Shanker511/GateWatch/assets/concepts/09-demo-sequence-concept.png

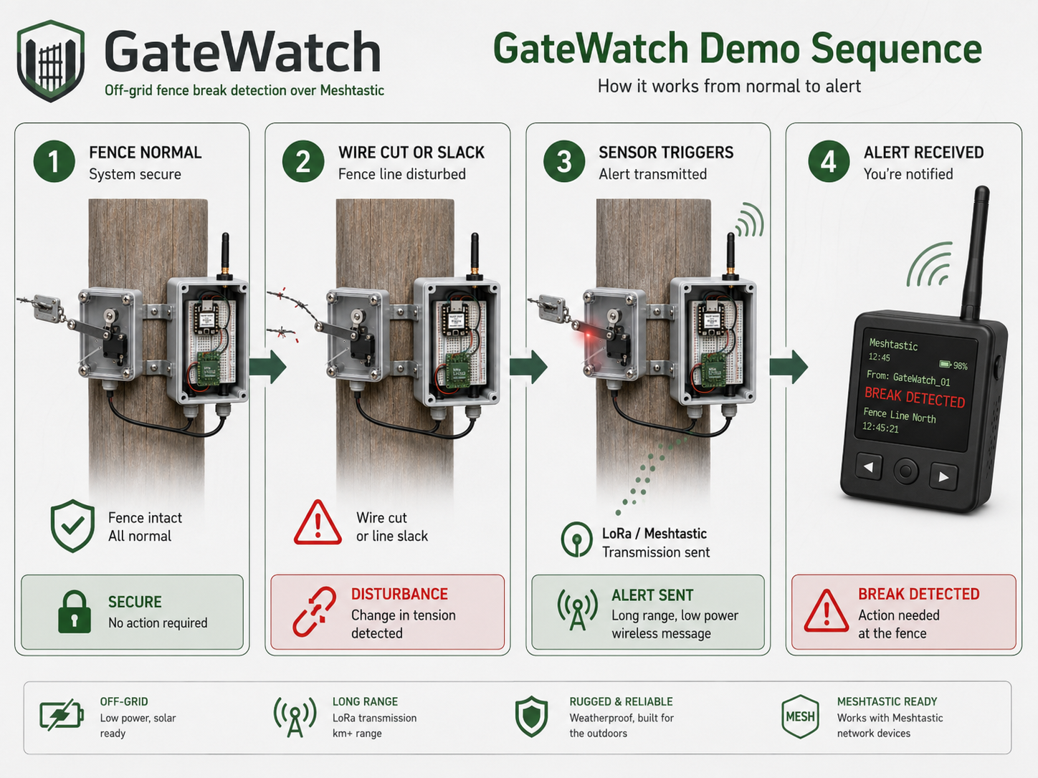
assets/concepts/09-demo-sequence-concept.png
