Shanker511/GateWatch/assets/concepts/10-farmer-use-concept.png

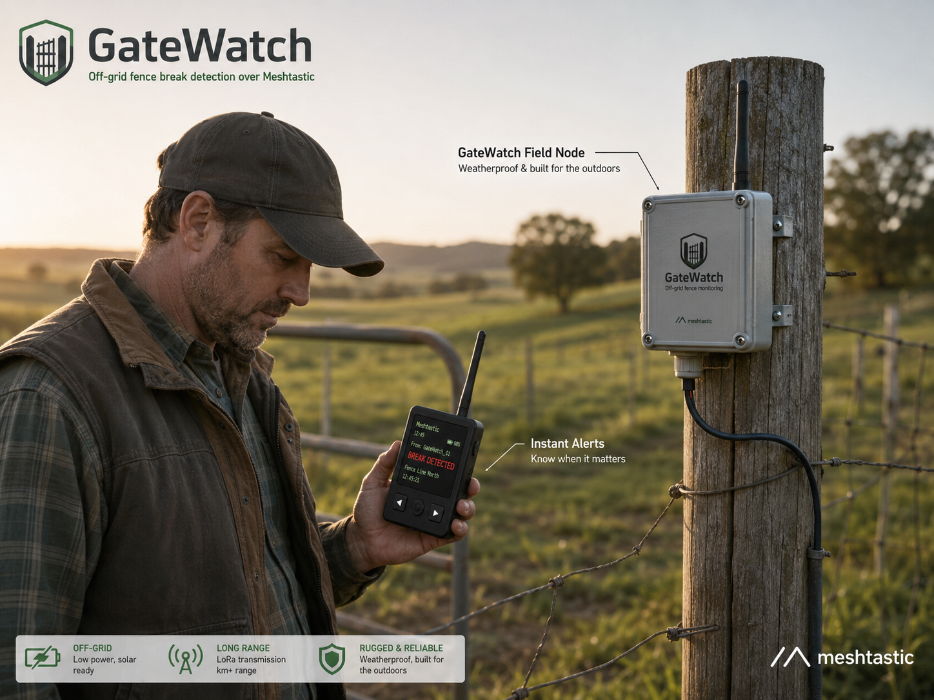
assets/concepts/10-farmer-use-concept.png
