Shanker511/GateWatch/assets/concepts/04-prototype-wiring-concept.png

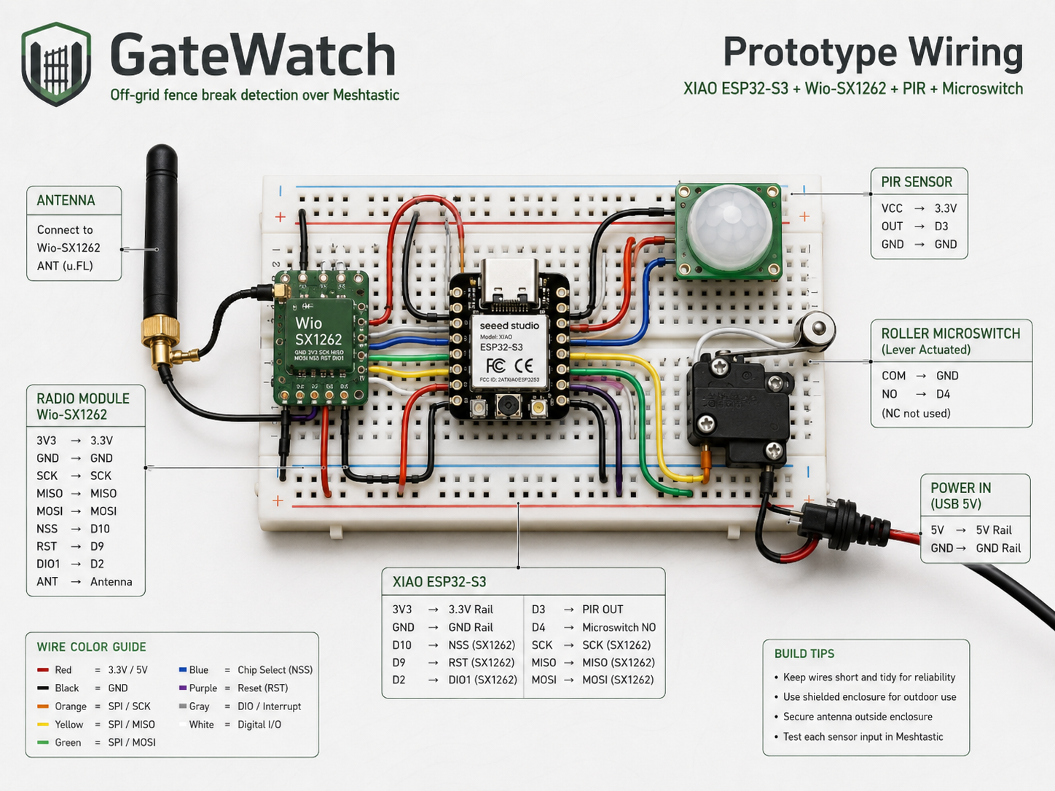
assets/concepts/04-prototype-wiring-concept.png
