Shanker511/GateWatch/hardware/gatewatch.kicad_sch

## KiCad design hardware/gatewatch.kicad_sch (2026-08-13)

Schematic: gatewatch.kicad_sch

Parts:
C1, C3, C4, C5, C6, C10: 100nF; C0805
C2, C7, C8, C9: 10uF; C0805
CN1: XT30UPB-M; CONN-TH_XT30UPB-M; MPN XT30UPB-M; LCSC C428721
CN2: B2B-PH-K-S; CONN-TH_B2B-PH-K-S; MPN B2B-PH-K-S(LF)(SN); LCSC C131337
D1: SS34_C8678; SMA_L4.3-W2.6-LS5.2-RD; MPN SS34; LCSC C8678
D2: SMAJ5.0A_C113952; SMA_L4.4-W2.6-LS5.0-RD; MPN SMAJ5.0A; LCSC C113952
F1: Fuse_Unspecified; Unspecified_Fuse_Package
J1: SMA_Amphenol_132134; Amphenol_132134_SMA_PCB_ThroughHole; MPN 132134
LED1: KT-0603R; LED-SMD_L1.6-W0.8-R-RD; MPN KT-0603R; LCSC C2286
R1: FSR402; Interlink_FSR402_Round_18.3x56.34mm; MPN 30-81794
R2, R3: 10k; R0805
R4: 2.4k; R0805
R5: 2k; R0805
R6, R7: 1k; R0805
SW1: HX 3X4X2.5-PA-4N PUSH BUTTON SWITCH; SW-SMD_4P-L4.2-W3.4-P2.15-LS5.2; MPN HX 3x4x2.5-PA-4N push button switch; LCSC C55200589
U1: ESP32-S3; QFN-56_L7.0-W7.0-P0.40-TL-EP4.0; MPN ESP32-S3; LCSC C2913192
U2: WIO-SX1262_C9900174795; COMM-SMD_12P-L11.6-W11.0-P1.27_114993390; MPN Wio-SX1262; LCSC C9900174795
U3: CN3163; ESOP-8_L4.9-W3.9-P1.27-LS6.0-BL-EP; MPN CN3163; LCSC C559031
U4: HC-SR501; PinHeader_1x03_P2.54mm_HC-SR501; MPN HC-SR501
U5: MagneticSwitch_Unspecified; ReedSwitch_THT_P10.00mm; MPN Unknown
U6: 发光二极管（黄绿色）; LED0805-RD; MPN 发光二极管（黄绿色）; LCSC C28105

Connections:
+3.3V: C1.1, C2.1, C3.1, C4.1, C5.1, C6.1, R6.2, R7.2, U1.2 (VDD3P3), U1.3 (VDD3P3), U1.20 (VDD3P3_RTC), U1.29 (VDD_SPI), U1.46 (VDD3P3_CPU), U1.55 (VDDA), U1.56 (VDDA), U2.8 (VCC)
BATT_FUSE: CN2.2, F1.1
GND: C1.2, C2.2, C3.2, C4.2, C5.2, C6.2, C7.2, C8.2, C9.2, C10.2, CN1.1 (-), CN2.1, D2.2, J1.3 (GND), J1.4 (GND), J1.5 (GND), R1.2 (TERM2), R4.1, R5.2, SW1.2, U1.57 (EP), U2.7 (GND), U2.10 (GND), U3.3 (GND), U3.9 (PAD), U4.3 (GND), U5.2 (SW2)
LORA_ANT: J1.1 (RF), U2.9 (ANT)
LORA_BUSY: U1.13 (GPIO8), U2.11 (BUSY)
LORA_DIO1: U1.12 (GPIO7), U2.12 (DIO1)
LORA_NRST: U1.14 (GPIO9), U2.5 (NRST)
LORA_NSS: U1.15 (GPIO10), U2.6 (NSS)
unnamed: C7.1, U3.4 (VIN)
unnamed: C9.1, U4.1 (VCC)
unnamed: C10.1, J1.2 (GND)
unnamed: LED1.1 (A), R6.1
unnamed: LED1.2 (K), U3.7 (~CHRG)
unnamed: R1.1 (TERM1), R3.1
unnamed: R2.1, U5.1 (SW1)
unnamed: R2.2, U1.7 (GPIO2)
unnamed: R3.2, U1.8 (GPIO3)
unnamed: R4.2, U3.2 (ISET)
unnamed: R5.1, U3.8 (FB)
unnamed: R7.1, U6.2 (A)
unnamed: U3.6 (~DONE), U6.1 (K)
PIR_OUT: U1.6 (GPIO1), U4.2 (OUT)
SOLAR_POS: CN1.2 (+), D1.2 (A)
SPI_MISO: U1.18 (GPIO13), U2.2 (MISO)
SPI_MOSI: U1.16 (GPIO11), U2.3 (MOSI)
SPI_SCK: U1.17 (GPIO12), U2.4 (SCK)
TAMPER_SW: SW1.1, U1.9 (GPIO4)
VBAT: C8.1, F1.2, U3.5 (BAT)

Notes on the sheet:
PROTOFLOW_REGION:eyJpZCI6ImU5ZDg3OTdmLWQzMjEtNDcxZC04OTM5LTkzYWUwYmQyMzRiNiIsIm5hbWUiOiJNaWNyb2NvbnRyb2xsZXIiLCJ4MSI6MTIuNywieTEiOjMxNy41LCJ4MiI6MTYyNS42LCJ5MiI6MTI3MC4wLCJjb2xvciI6NDI4NTUwNzgwNCwiZGVzY3JpcHRpb24iOm51bGwsImNvbXBvbmVudElkcyI6WyIxMzQ1NjA2NC1iNmY4LTQyMmMtYTdiZi01OWEzYmU1MGY1NmYiLCI0Mz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
Microcontroller
PROTOFLOW_REGION:eyJpZCI6ImI1YWU3MWIzLWIxNDYtNDQ0NC04YjI0LWMxZWRjOTRlZmI5ZiIsIm5hbWUiOiJMb1JhIFJhZGlvIiwieDEiOjE5MTcuNjk5OTk5OTk5OTk5OCwieTEiOjU4NC4xOTk5OTk5OTk5OTk5LCJ4MiI6MjU1Mi43LCJ5MiI6MTA0MS4zOTk5OTk5OTk5OTk5LCJjb2xvciI6NDI4NTUwNzgwNCwiZGVzY3JpcHRpb24iOm51bGwsImNvbXBvbmVudElkcyI6WyI4YjM4ODkzMy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
LoRa Radio
PROTOFLOW_REGION:eyJpZCI6ImQ5OWM2OTY2LTE2M2EtNGNmNC1iNTQ3LWEwOGNjYzcxMjNkZCIsIm5hbWUiOiJTb2xhciAmIEJhdHRlcnkgTWFuYWdlbWVudCIsIngxIjozMTg3LjcsInkxIjo1NDYuMSwieDIiOjQ0OTUuOCwieTIiOjEwMDMuMywiY29sb3IiOjQyODU1MDc4MDQsImRlc2NyaXB0aW9uIjpudWxsLCJjb21wb25lbnRJZHMiOlsiYzMxMjNhZjctZjYwMy00NmM0LTg2Y2QtYzU2NW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
Solar & Battery Management
PROTOFLOW_REGION:eyJpZCI6ImQyZTU5MGNjLTBlMTgtNGMxOC1iMmYxLWM1MDFmNGQ0MGMyZCIsIm5hbWUiOiJTb2xhciAmIEJhdHRlcnkgTWFuYWdlbWVudCIsIngxIjo2MDkuNTk5OTk5OTk5OTk5OSwieTEiOjE4NjYuODk5OTk5OTk5OTk5OSwieDIiOjExODEuMSwieTIiOjIwNzAuMSwiY29sb3IiOjQyODU1MDc4MDQsImRlc2NyaXB0aW9uIjpudWxsLCJjb21wb25lbnRJZHMiOlsiOGFlZD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
PROTOFLOW_REGION:eyJpZCI6ImNjZjc2NTg0LTI5N2YtNGYxOC1hZTA1LTRmODYxM2UzYzhkMyIsIm5hbWUiOiJTb2xhciAmIEJhdHRlcnkgTWFuYWdlbWVudCIsIngxIjoyMTcxLjcsInkxIjoxODI4LjgsIngyIjoyNzQzLjIsInkyIjoyMDgyLjc5OTk5OTk5OTk5OTcsImNvbG9yIjo0Mjg1NTA3ODA0LCJkZXNjcmlwdGlvbiI6bnVsbCwiY29tcG9uZW50SWRzIjpbIjRjMjIxNDMwLTg1MmUtNG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
PROTOFLOW_REGION:eyJpZCI6IjYzOTAxYmJiLTkxMmEtNGVmYy1hNGIyLWI5NDlkZGY5YTZjMiIsIm5hbWUiOiJGZW5jZSAmIE1vdGlvbiBTZW5zb3JzIiwieDEiOjM1NTYuMCwieTEiOjE3NzguMCwieDIiOjQwNTEuMjk5OTk5OTk5OTk5NywieTIiOjIxNzEuNywiY29sb3IiOjQyODU1MDc4MDQsImRlc2NyaXB0aW9uIjpudWxsLCJjb21wb25lbnRJZHMiOlsiMjA5ZTkyNDYtY2NlOS00OTIxLW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
Fence & Motion Sensors
PROTOFLOW_REGION:eyJpZCI6IjA4NzYzNjc2LWMyOWMtNGVlOS1iNGI4LTMwOTIwM2ZiNzc4ZSIsIm5hbWUiOiJMb1JhIFJhZGlvIiwieDEiOjUwLjgsInkxIjozMDA5Ljg5OTk5OTk5OTk5OTYsIngyIjoxMjU3LjMsInkyIjo0MDM4LjYsImNvbG9yIjo0Mjg1NTA3ODA0LCJkZXNjcmlwdGlvbiI6bnVsbCwiY29tcG9uZW50SWRzIjpbImY0ZmY3YTBjLTM4ZWQtNDk5NS04OWZhLWMyYzg4NDBkMD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
